chrisjohnson1988/eddie/receiver.cpp

#include <RF24/RF24.h>
#include <RF24Network/RF24Network.h>
#include <cstdlib>
#include <iostream>
#include <cmath>
#include <stdio.h>
#include <curl/curl.h>
#include <sstream>
#include <sys/wait.h>
#include <unistd.h>

RF24 radio(RPI_V2_GPIO_P1_15, BCM2835_SPI_CS0, BCM2835_SPI_SPEED_8MHZ);
RF24Network network(radio);

const int RESET_RADIO_AFTER_NO_PACKET = 30;
const uint16_t MY_ADDR = 00;
const uint16_t EDDIE_ADDR = 01;
const uint16_t MINI_EDDIE_ADDR = 011;

struct Payload {
  float in_temp;
  float in_hum;
  float out_temp;
  float out_hum;
  float voltage;
  uint16_t soil1;
  uint16_t soil2;
};

struct PayloadRemoteSoil {
  float voltage;
  uint16_t soil1;
};

void initRadio() {
  radio.begin();
  radio.enableDynamicPayloads();
  radio.setAutoAck(1);
  radio.setRetries(15,15);
  radio.setDataRate(RF24_250KBPS);
  radio.setPALevel(RF24_PA_MAX);
  radio.setCRCLength(RF24_CRC_8);
  network.begin(108, MY_ADDR);
}

/**
 * Start looping listening to packets from the NRF24 radio. If one is received
 * from the arduino sensor node then submit its values to thingspeak
 */
int receive(char* eddie_key, char* mini_eddie_key) {
  initRadio();
  radio.printDetails();
  curl_global_init(CURL_GLOBAL_ALL);
  CURL *curl;
  curl = curl_easy_init();
  int lastreceived = 0;

  while(1) {
    network.update();

    while ( network.available() ) {
      RF24NetworkHeader header;
      network.peek(header);
      lastreceived = 0; //reset radio no packet count

      if(header.from_node == EDDIE_ADDR) {
        Payload payload;
        network.read(header,&payload,sizeof(payload));
        std::stringstream data;
        data << "https://api.thingspeak.com/update"
             << "?api_key=" << eddie_key
             << "&field1="  << payload.in_temp
             << "&field2="  << payload.in_hum
             << "&field3="  << payload.out_temp
             << "&field4="  << payload.out_hum
             << "&field5="  << payload.voltage
             << "&field6="  << payload.soil1
             << "&field7="  << payload.soil2;

        curl_easy_setopt(curl, CURLOPT_URL, data.str().c_str());
        curl_easy_perform(curl);
        std::cout << " Eddie Packet Sent\n";
      }
      if(header.from_node == MINI_EDDIE_ADDR) {
        PayloadRemoteSoil payload;
        network.read(header,&payload,sizeof(payload));
        std::stringstream data;
        data << "https://api.thingspeak.com/update"
             << "?api_key=" << mini_eddie_key
             << "&field1="  << payload.voltage
             << "&field2="  << payload.soil1;

        curl_easy_setopt(curl, CURLOPT_URL, data.str().c_str());
        curl_easy_perform(curl);
        std::cout << " Mini Eddie Packet Sent\n";
      }
    }
    if(lastreceived++ > RESET_RADIO_AFTER_NO_PACKET) {
      std::cout << "No packets for a while. Killing radio for reset\n";
      return EXIT_FAILURE;
    }
    delay(2000);
  }
  curl_global_cleanup();
  return EXIT_SUCCESS;
}

/**
 * Run the receive function with a watchdog incase of premature failure. If the
 * receive function dies (lack of packets), the watchdog can restart in a fresh 
 * process.
 */
int main(int argc, char *argv[]) {
  char* eddie_key      = std::getenv("EDDIE_API_KEY");
  char* mini_eddie_key = std::getenv("MINI_EDDIE_API_KEY");
  if(eddie_key && mini_eddie_key) {
    while(1) {
      pid_t pid = fork();
      if(pid == 0) {
        return receive(eddie_key, mini_eddie_key);
      }
      else {
        int status;
        wait(&status);
        delay(10000);
        std::cout << "Watchdog Restarting\n";
      }
    }
  }
  std::cout << "Expected to find EDDIE_API_KEY and MINI_EDDIE_API_KEY environment variables to be defined\n";
  return EXIT_FAILURE;
}
